stephenwhittle/psx_sio_connectors/img/20250620_124911.jpg

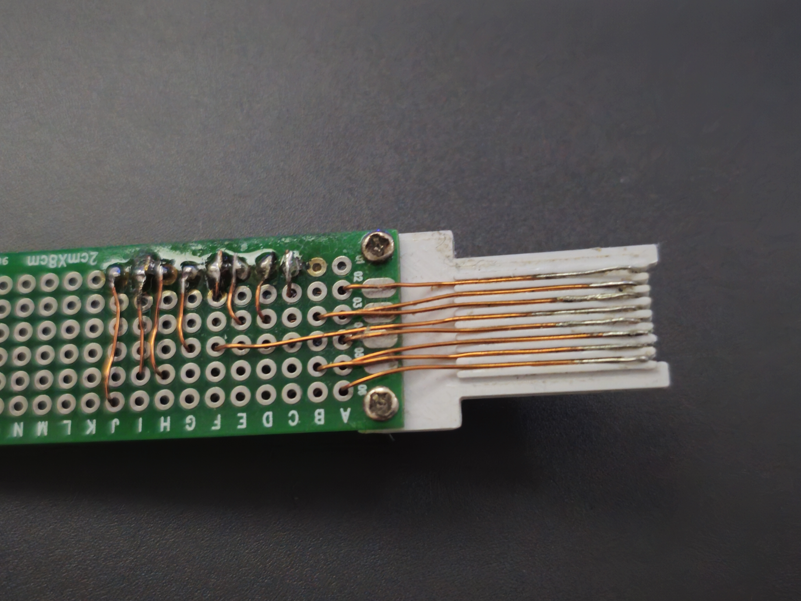
img/20250620_124911.jpg
