stephenwhittle/psx_sio_connectors/img/20250620_133352.jpg

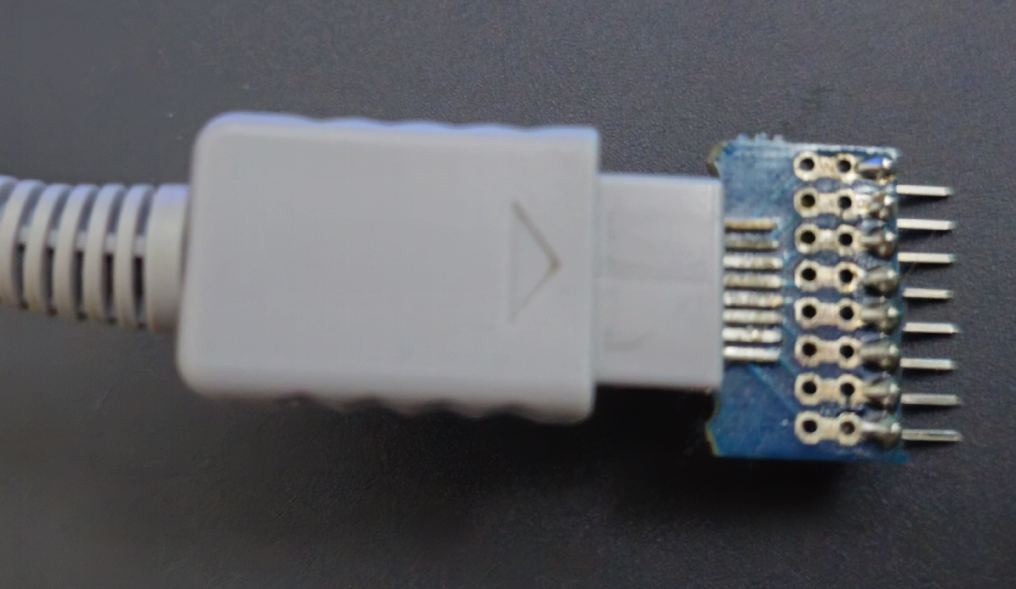
img/20250620_133352.jpg
